lordswift/BambuHelper/src/clock_pong.h

#ifndef CLOCK_PONG_H
#define CLOCK_PONG_H

// Pong/Breakout animated clock - call tickPongClock() from loop()
void tickPongClock();

// Reset state (call when entering SCREEN_CLOCK)
void resetPongClock();

#endif // CLOCK_PONG_H
