lordswift/BambuHelper/src/display_ui.cpp

#include "display_ui.h"
#include "display_gauges.h"
#include "display_anim.h"
#include "clock_mode.h"
#include "clock_pong.h"
#include "icons.h"
#include "config.h"
#include "layout.h"
#include "bambu_state.h"
#include "bambu_mqtt.h"
#include "settings.h"
#include "tasmota.h"
#include <WiFi.h>
#include <time.h>

TFT_eSPI tft = TFT_eSPI();

// Use user-configured bg color instead of hardcoded CLR_BG
#undef  CLR_BG
#define CLR_BG  (dispSettings.bgColor)

static ScreenState currentScreen = SCREEN_SPLASH;
static ScreenState prevScreen = SCREEN_SPLASH;
static bool forceRedraw = true;
static unsigned long lastDisplayUpdate = 0;

// Previous state for smart redraw
static BambuState prevState;
static bool prevWaitingForDoor = false;
static unsigned long connectScreenStart = 0;

// ---------------------------------------------------------------------------
//  Smooth gauge interpolation - values lerp toward MQTT actuals each frame
// ---------------------------------------------------------------------------
static float smoothNozzleTemp   = 0;
static float smoothBedTemp      = 0;
static float smoothPartFan     = 0;
static float smoothAuxFan      = 0;
static float smoothChamberFan  = 0;
static float smoothChamberTemp = 0;
static float smoothHeatbreakFan= 0;
static bool  smoothInited      = false;

static bool gaugesAnimating = false;       // true while arcs are interpolating
static const unsigned long GAUGE_ANIM_MS = 80; // ~12 Hz during animation

static const float SMOOTH_ALPHA = 0.09f;  // per frame at 12Hz — ~1s to settle
static const float SNAP_THRESH  = 0.5f;   // snap when within 0.5 of target

static void smoothLerp(float& cur, float target) {
  float diff = target - cur;
  if (fabsf(diff) < SNAP_THRESH) cur = target;
  else cur += diff * SMOOTH_ALPHA;
}

// Returns true if any gauge is still animating
static bool tickGaugeSmooth(const BambuState& s, bool snap) {
  if (snap || !smoothInited) {
    smoothNozzleTemp   = s.nozzleTemp;
    smoothBedTemp      = s.bedTemp;
    smoothPartFan      = s.coolingFanPct;
    smoothAuxFan       = s.auxFanPct;
    smoothChamberFan   = s.chamberFanPct;
    smoothChamberTemp  = s.chamberTemp;
    smoothHeatbreakFan = s.heatbreakFanPct;
    smoothInited = true;
    return false;
  }
  smoothLerp(smoothNozzleTemp,   s.nozzleTemp);
  smoothLerp(smoothBedTemp,      s.bedTemp);
  smoothLerp(smoothPartFan,      (float)s.coolingFanPct);
  smoothLerp(smoothAuxFan,       (float)s.auxFanPct);
  smoothLerp(smoothChamberFan,   (float)s.chamberFanPct);
  smoothLerp(smoothChamberTemp,  s.chamberTemp);
  smoothLerp(smoothHeatbreakFan, (float)s.heatbreakFanPct);

  const float ANIM_EPS = 0.01f;
  return (fabsf(smoothNozzleTemp   - s.nozzleTemp)              > ANIM_EPS) ||
         (fabsf(smoothBedTemp      - s.bedTemp)                 > ANIM_EPS) ||
         (fabsf(smoothPartFan      - (float)s.coolingFanPct)    > ANIM_EPS) ||
         (fabsf(smoothAuxFan       - (float)s.auxFanPct)        > ANIM_EPS) ||
         (fabsf(smoothChamberFan   - (float)s.chamberFanPct)    > ANIM_EPS) ||
         (fabsf(smoothChamberTemp  - s.chamberTemp)             > ANIM_EPS) ||
         (fabsf(smoothHeatbreakFan - (float)s.heatbreakFanPct)  > ANIM_EPS);
}

// ---------------------------------------------------------------------------
//  Backlight
// ---------------------------------------------------------------------------
static uint8_t lastAppliedBrightness = 0;

void setBacklight(uint8_t level) {
#if defined(BACKLIGHT_PIN) && BACKLIGHT_PIN >= 0
#if defined(DISPLAY_1_8)
  digitalWrite(BACKLIGHT_PIN, level > 0 ? LOW : HIGH);  // Active low backlight
#else
  analogWrite(BACKLIGHT_PIN, level);
#endif
#endif
  lastAppliedBrightness = level;
}

// ---------------------------------------------------------------------------
//  Init
// ---------------------------------------------------------------------------
void initDisplay() {
  Serial.println("Display: pre-init delay...");
  delay(500);
  Serial.println("Display: calling tft.init()...");
  Serial.flush();
  tft.init();  // TFT_eSPI configures SPI from build flags
  Serial.println("Display: tft.init() done");
#if defined(DISPLAY_CYD)
  // Clear entire GRAM at rotation 0 first (guarantees all 240x320 pixels
  // are addressed). Without this, rotations 1/3 leave 80px of uninitialized
  // VRAM visible as garbage noise on the extra screen edge.
  tft.setRotation(0);
  tft.fillScreen(TFT_BLACK);
#endif
  tft.setRotation(dispSettings.rotation);
#if defined(DISPLAY_CYD)
  if (dispSettings.invertColors) tft.invertDisplay(false);
#endif
  Serial.println("Display: setRotation done");
  tft.fillScreen(CLR_BG);
  Serial.println("Display: fillScreen done");

#if defined(TOUCH_CS) && !defined(USE_XPT2046)
  uint16_t calData[5] = {321, 3498, 280, 3584, 3};
  tft.setTouch(calData);
  Serial.println("Display: touch calibration set");
#endif

#if defined(BACKLIGHT_PIN) && BACKLIGHT_PIN >= 0
  pinMode(BACKLIGHT_PIN, OUTPUT);
  setBacklight(200);
#endif

  memset(&prevState, 0, sizeof(prevState));

  // Splash screen
  tft.setTextDatum(MC_DATUM);
  tft.setTextColor(CLR_GREEN, CLR_BG);
  tft.setTextFont(3);
  tft.drawString("BambuHelper", SCREEN_W / 2, SCREEN_H / 2 - 24);
  tft.setTextFont(2);
  tft.setTextColor(CLR_TEXT_DIM, CLR_BG);
  tft.drawString("Printer Monitor", SCREEN_W / 2, SCREEN_H / 2 - 2);
  tft.setTextFont(1);
  tft.drawString(FW_VERSION, SCREEN_W / 2, SCREEN_H / 2 + 16);
}

void applyDisplaySettings() {
#if defined(DISPLAY_CYD)
  // Pre-clear entire GRAM at rotation 0 to prevent garbage on edges
  tft.setRotation(0);
  tft.fillScreen(TFT_BLACK);
#endif
  tft.setRotation(dispSettings.rotation);
#if defined(DISPLAY_CYD)
  tft.invertDisplay(dispSettings.invertColors ? false : true);
#endif
  tft.fillScreen(dispSettings.bgColor);
  forceRedraw = true;
  lastDisplayUpdate = 0;  // bypass throttle so redraw is immediate after fillScreen
  // Reset clock/pong so they redraw fully after fillScreen cleared everything
  if (currentScreen == SCREEN_CLOCK) {
    if (dispSettings.pongClock) resetPongClock();
    else resetClock();
  }
}

void triggerDisplayTransition() {
  // Clear previous state so everything redraws for the new printer
  memset(&prevState, 0, sizeof(prevState));
  smoothInited = false;  // snap gauges to new printer's values
  resetGaugeTextCache();
  tft.fillScreen(dispSettings.bgColor);
  forceRedraw = true;
}

void setScreenState(ScreenState state) {
  currentScreen = state;
}

ScreenState getScreenState() {
  return currentScreen;
}

// ---------------------------------------------------------------------------
//  Nozzle label helper (dual nozzle H2D/H2C)
// ---------------------------------------------------------------------------
static const char* nozzleLabel(const BambuState& s) {
  if (!s.dualNozzle) return "Nozzle";
  return s.activeNozzle == 0 ? "Nozzle R" : "Nozzle L";
}

// ---------------------------------------------------------------------------
//  Speed level name helper
// ---------------------------------------------------------------------------
static const char* speedLevelName(uint8_t level) {
  switch (level) {
    case 1: return "Silent";
    case 2: return "Std";
    case 3: return "Sport";
    case 4: return "Ludicr";
    default: return "---";
  }
}

static uint16_t speedLevelColor(uint8_t level) {
  switch (level) {
    case 1: return CLR_BLUE;
    case 2: return CLR_GREEN;
    case 3: return CLR_ORANGE;
    case 4: return CLR_RED;
    default: return CLR_TEXT_DIM;
  }
}

// ---------------------------------------------------------------------------
//  Screen: AP Mode
// ---------------------------------------------------------------------------
static void drawAPMode() {
  tft.setTextDatum(MC_DATUM);

  // Title
  tft.setTextColor(CLR_GREEN, CLR_BG);
  tft.setTextFont(3);
  tft.drawString("WiFi Setup", SCREEN_W / 2, LY_AP_TITLE_Y);

  // Instructions
  tft.setTextFont(1);
  tft.setTextColor(CLR_TEXT, CLR_BG);
  tft.drawString("Connect to WiFi:", SCREEN_W / 2, LY_AP_SSID_LBL_Y);

  // AP SSID
  tft.setTextColor(CLR_CYAN, CLR_BG);
  tft.setTextFont(3);
  char ssid[32];
  uint32_t mac = (uint32_t)(ESP.getEfuseMac() & 0xFFFF);
  snprintf(ssid, sizeof(ssid), "%s%04X", WIFI_AP_PREFIX, mac);
  tft.drawString(ssid, SCREEN_W / 2, LY_AP_SSID_Y);

  // Password
  tft.setTextFont(1);
  tft.setTextColor(CLR_TEXT_DIM, CLR_BG);
  tft.drawString("Password:", SCREEN_W / 2, LY_AP_PASS_LBL_Y);
  tft.setTextColor(CLR_TEXT, CLR_BG);
  tft.drawString(WIFI_AP_PASSWORD, SCREEN_W / 2, LY_AP_PASS_Y);

  // IP
  tft.setTextColor(CLR_TEXT_DIM, CLR_BG);
  tft.drawString("Then open:", SCREEN_W / 2, LY_AP_OPEN_Y);
  tft.setTextColor(CLR_ORANGE, CLR_BG);
  tft.setTextFont(3);
  tft.drawString("192.168.4.1", SCREEN_W / 2, LY_AP_IP_Y);
}

// ---------------------------------------------------------------------------
//  Screen: Connecting WiFi
// ---------------------------------------------------------------------------
static void drawConnectingWiFi() {
  tft.setTextDatum(MC_DATUM);

  // Title
  tft.setTextFont(1);
  tft.setTextColor(CLR_TEXT, CLR_BG);
  tft.drawString("Connecting to WiFi", SCREEN_W / 2, SCREEN_H / 2 - 24);

  int16_t tw = tft.textWidth("Connecting to WiFi");
  drawAnimDots(tft, SCREEN_W / 2 + tw / 2, SCREEN_H / 2 - 30, CLR_TEXT);

  // Slide bar
  const int16_t barW = 96;
  const int16_t barH = 6;
  drawSlideBar(tft, (SCREEN_W - barW) / 2, SCREEN_H / 2 + 12,
               barW, barH, CLR_BLUE, CLR_TRACK);
}

// ---------------------------------------------------------------------------
//  Screen: WiFi Connected (show IP)
// ---------------------------------------------------------------------------
static void drawWiFiConnected() {
  if (!forceRedraw) return;

  tft.setTextDatum(MC_DATUM);

  // Checkmark circle with tick
  int cx = SCREEN_W / 2;
  int cy = SCREEN_H / 2 - 40;
  tft.fillCircle(cx, cy, 18, CLR_GREEN);
  // Draw thick tick mark (2px wide)
  for (int i = -1; i <= 1; i++) {
    tft.drawLine(cx - 12, cy + i,     cx - 4, cy + 8 + i, CLR_BG);  // short leg
    tft.drawLine(cx - 4,  cy + 8 + i, cx + 12, cy - 6 + i, CLR_BG); // long leg
  }

  tft.setTextColor(CLR_GREEN, CLR_BG);
  tft.setTextFont(3);
  tft.drawString("WiFi Connected", SCREEN_W / 2, SCREEN_H / 2 + 8);

  tft.setTextColor(CLR_TEXT, CLR_BG);
  tft.setTextFont(1);
  tft.drawString(WiFi.localIP().toString().c_str(), SCREEN_W / 2, SCREEN_H / 2 + 28);
}

// ---------------------------------------------------------------------------
//  Screen: OTA firmware update in progress
// ---------------------------------------------------------------------------
#ifdef ENABLE_OTA_AUTO
#include "web_server.h"
static void drawOtaUpdate() {
  tft.setTextDatum(MC_DATUM);
  tft.setTextColor(CLR_TEXT, CLR_BG);

  // Title
  tft.setTextFont(3);
  tft.drawString("Updating", SCREEN_W / 2, SCREEN_H / 2 - 50);
  tft.setTextFont(2);
  tft.setTextColor(CLR_TEXT_DIM, CLR_BG);
  tft.drawString("BambuHelper firmware", SCREEN_W / 2, SCREEN_H / 2 - 26);

  // Progress bar
  int pct = getOtaAutoProgress();
  const int16_t barX = 16, barY = SCREEN_H / 2 - 8;
  const int16_t barW = SCREEN_W - 32, barH = 10;
  tft.fillRoundRect(barX, barY, barW, barH, 4, CLR_TRACK);
  if (pct > 0) {
    int16_t fill = (int16_t)((pct / 100.0f) * barW);
    tft.fillRoundRect(barX, barY, fill, barH, 4, CLR_GREEN);
  }

  // Percentage
  char pctBuf[8];
  snprintf(pctBuf, sizeof(pctBuf), "%d%%", pct);
  tft.setTextFont(2);
  tft.setTextColor(CLR_TEXT, CLR_BG);
  tft.drawString(pctBuf, SCREEN_W / 2, SCREEN_H / 2 + 14);

  // Status
  tft.setTextFont(2);
  tft.setTextColor(CLR_TEXT_DIM, CLR_BG);
  tft.drawString(getOtaAutoStatus(), SCREEN_W / 2, SCREEN_H / 2 + 34);

  // Warning
  tft.setTextColor(CLR_ORANGE, CLR_BG);
  tft.drawString("Do not power off", SCREEN_W / 2, SCREEN_H / 2 + 58);
}
#endif // ENABLE_OTA_AUTO

// ---------------------------------------------------------------------------
//  Screen: Connecting MQTT
// ---------------------------------------------------------------------------
static void drawConnectingMQTT() {
  tft.setTextDatum(MC_DATUM);

  // Title
  tft.setTextFont(2);
  tft.setTextColor(CLR_TEXT, CLR_BG);
  tft.drawString("Connecting to Printer", SCREEN_W / 2, SCREEN_H / 2 - 40);

  int16_t tw = tft.textWidth("Connecting to Printer");
  drawAnimDots(tft, SCREEN_W / 2 + tw / 2, SCREEN_H / 2 - 46, CLR_TEXT);
  tft.setTextDatum(MC_DATUM);

  // Slide bar
  const int16_t barW = 96;
  const int16_t barH = 6;
  drawSlideBar(tft, (SCREEN_W - barW) / 2, SCREEN_H / 2 - 12,
               barW, barH, CLR_ORANGE, CLR_TRACK);

  // Connection mode + printer info
  PrinterSlot& p = displayedPrinter();
  tft.setTextColor(CLR_TEXT_DIM, CLR_BG);
  tft.setTextFont(2);

  const char* modeStr = isCloudMode(p.config.mode) ? "Cloud" : "LAN";
  char infoBuf[40];
  if (isCloudMode(p.config.mode)) {
    snprintf(infoBuf, sizeof(infoBuf), "[%s] %s", modeStr,
             strlen(p.config.serial) > 0 ? p.config.serial : "no serial!");
  } else {
    snprintf(infoBuf, sizeof(infoBuf), "[%s] %s",  modeStr,
             strlen(p.config.ip) > 0 ? p.config.ip : "no IP!");
  }
  tft.drawString(infoBuf, SCREEN_W / 2, SCREEN_H / 2 + 10);

  // Elapsed time
  if (connectScreenStart > 0) {
    unsigned long elapsed = (millis() - connectScreenStart) / 1000;
    char elBuf[16];
    snprintf(elBuf, sizeof(elBuf), "%lus", elapsed);
    tft.fillRect(SCREEN_W / 2 - 30, SCREEN_H / 2 + 22, 60, 16, CLR_BG);
    tft.drawString(elBuf, SCREEN_W / 2, SCREEN_H / 2 + 30);
  }

  // Diagnostics (only after first attempt)
  const MqttDiag& d = getMqttDiag(rotState.displayIndex);
  if (d.attempts > 0) {
    tft.setTextFont(1);
    tft.setTextDatum(MC_DATUM);

    char buf[40];
    snprintf(buf, sizeof(buf), "Attempt: %u", d.attempts);
    tft.setTextColor(CLR_TEXT_DIM, CLR_BG);
    tft.drawString(buf, SCREEN_W / 2, SCREEN_H / 2 + 50);

    if (d.lastRc != 0) {
      snprintf(buf, sizeof(buf), "Err: %s", mqttRcToString(d.lastRc));
      tft.setTextColor(CLR_RED, CLR_BG);
      tft.drawString(buf, SCREEN_W / 2, SCREEN_H / 2 + 62);
    }
  }
}

// Forward declaration (defined after CYD section)
static void drawWifiSignalIndicator(const BambuState& s, int16_t wifiY);

// ---------------------------------------------------------------------------
//  Screen: Idle (connected, not printing)
// ---------------------------------------------------------------------------
static void drawIdleNoPrinter() {
  if (!forceRedraw) return;

  tft.setTextDatum(MC_DATUM);

  tft.setTextColor(CLR_GREEN, CLR_BG);
  tft.setTextFont(3);
  tft.drawString("BambuHelper", SCREEN_W / 2, LY_IDLE_NP_TITLE_Y);

  tft.setTextColor(CLR_TEXT, CLR_BG);
  tft.setTextFont(2);
  tft.drawString("WiFi Connected", SCREEN_W / 2, LY_IDLE_NP_WIFI_Y);

  tft.fillCircle(SCREEN_W / 2, LY_IDLE_NP_DOT_Y, 5, CLR_GREEN);

  tft.setTextColor(CLR_TEXT_DIM, CLR_BG);
  tft.setTextFont(1);
  tft.drawString("No printer configured", SCREEN_W / 2, LY_IDLE_NP_MSG_Y);
  tft.drawString("Open in browser:", SCREEN_W / 2, LY_IDLE_NP_OPEN_Y);

  tft.setTextColor(CLR_ORANGE, CLR_BG);
  tft.setTextFont(3);
  tft.drawString(WiFi.localIP().toString().c_str(), SCREEN_W / 2, LY_IDLE_NP_IP_Y);
}

static bool wasNoPrinter = false;

static void drawIdle() {
  if (!isAnyPrinterConfigured()) {
    wasNoPrinter = true;
    drawIdleNoPrinter();
    return;
  }

  // Transition from "no printer" to configured — clear stale screen
  if (wasNoPrinter) {
    wasNoPrinter = false;
    tft.fillScreen(dispSettings.bgColor);
    memset(&prevState, 0, sizeof(prevState));
    forceRedraw = true;
  }

  PrinterSlot& p = displayedPrinter();
  BambuState& s = p.state;

  // Effective screen dimensions — idle uses full screen (no AMS sidebar)
#if defined(DISPLAY_CYD)
  const int16_t scrW = (int16_t)tft.width();
  const int16_t scrH = (int16_t)tft.height();
#else
  const int16_t scrW = SCREEN_W;
  const int16_t scrH = SCREEN_H;
#endif
  const int16_t cx = scrW / 2;

  bool animating = tickGaugeSmooth(s, forceRedraw);
  gaugesAnimating = animating;
  bool stateChanged = forceRedraw || (strcmp(s.gcodeState, prevState.gcodeState) != 0);
  bool tempChanged = forceRedraw || animating ||
                     (s.nozzleTemp != prevState.nozzleTemp) ||
                     (s.nozzleTarget != prevState.nozzleTarget) ||
                     (s.bedTemp != prevState.bedTemp) ||
                     (s.bedTarget != prevState.bedTarget);
  bool connChanged = forceRedraw || (s.connected != prevState.connected);
  bool wifiChanged = forceRedraw || (s.wifiSignal != prevState.wifiSignal);

  tft.setTextDatum(MC_DATUM);

  // Printer name (only on forceRedraw — name doesn't change)
  if (forceRedraw) {
    tft.setTextColor(CLR_GREEN, CLR_BG);
    tft.setTextFont(4);
    const char* name = (p.config.name[0] != '\0') ? p.config.name : "Bambu P1S";
    tft.drawString(name, cx, LY_IDLE_NAME_Y);
  }

  // Status badge — only redraw when state changes
  if (stateChanged) {
    tft.setTextFont(2);
    uint16_t stateColor = CLR_TEXT_DIM;
    const char* stateStr = s.gcodeState;
    if (strcmp(s.gcodeState, "IDLE") == 0) {
      stateColor = CLR_GREEN;
      stateStr = "Ready";
    } else if (strcmp(s.gcodeState, "FAILED") == 0) {
      stateColor = CLR_RED;
      stateStr = "ERROR";
    } else if (strcmp(s.gcodeState, "UNKNOWN") == 0 || s.gcodeState[0] == '\0') {
      stateStr = "Waiting...";
    }
    tft.fillRect(0, LY_IDLE_STATE_Y, scrW, LY_IDLE_STATE_H, CLR_BG);
    tft.setTextColor(stateColor, CLR_BG);
    tft.drawString(stateStr, cx, LY_IDLE_STATE_TY);
  }

  // Connected indicator
  if (connChanged) {
    tft.fillCircle(cx, LY_IDLE_DOT_Y, 5, s.connected ? CLR_GREEN : CLR_RED);
  }

  // "Press to refresh" hint for cloud printers stuck in UNKNOWN state
  {
    static unsigned long unknownSinceMs = 0;
    static bool hintShown = false;
    bool isUnknown = (strcmp(s.gcodeState, "UNKNOWN") == 0);
    if (isUnknown && unknownSinceMs == 0) unknownSinceMs = millis();
    if (!isUnknown) unknownSinceMs = 0;
    bool showHint = isUnknown && unknownSinceMs > 0 &&
                    millis() - unknownSinceMs > 60000 &&
                    buttonType != BTN_DISABLED &&
                    isCloudMode(p.config.mode) && s.connected;
    if (stateChanged || showHint != hintShown) {
      const int16_t hintY = LY_IDLE_DOT_Y + 15;
      tft.fillRect(0, hintY - 6, scrW, 14, CLR_BG);
      if (showHint) {
        tft.setTextFont(1);
        tft.setTextDatum(MC_DATUM);
        tft.setTextColor(CLR_TEXT_DARK, CLR_BG);
        tft.drawString("Press to refresh", cx, hintY);
      }
      hintShown = showHint;
    }
  }

  // Nozzle temp gauge
  if (tempChanged) {
    drawTempGauge(tft, cx - LY_IDLE_G_OFFSET, LY_IDLE_GAUGE_Y, LY_IDLE_GAUGE_R,
                  s.nozzleTemp, s.nozzleTarget, 300.0f,
                  dispSettings.nozzle.arc, nozzleLabel(s), nullptr, forceRedraw,
                  &dispSettings.nozzle, smoothNozzleTemp);

    // Bed temp gauge
    drawTempGauge(tft, cx + LY_IDLE_G_OFFSET, LY_IDLE_GAUGE_Y, LY_IDLE_GAUGE_R,
                  s.bedTemp, s.bedTarget, 120.0f,
                  dispSettings.bed.arc, "Bed", nullptr, forceRedraw,
                  &dispSettings.bed, smoothBedTemp);
  }

  // Bottom status bar: Filament/WiFi | Power | Door
  static bool     idlePrevTasmotaOnline = false;
  static float    idlePrevWatts        = -2.0f;

  bool idleTasmotaOnline = tasmotaIsActiveForSlot(rotState.displayIndex);
  float idleCurWatts = tasmotaGetWatts();

  int16_t botCY = scrH - 9;
  bool bottomChanged = wifiChanged ||
                       (s.ams.activeTray != prevState.ams.activeTray) ||
                       (s.doorOpen != prevState.doorOpen) ||
                       (s.doorSensorPresent != prevState.doorSensorPresent) ||
                       (tasmotaSettings.enabled && (idleTasmotaOnline != idlePrevTasmotaOnline ||
                                                    idleCurWatts != idlePrevWatts));
  idlePrevTasmotaOnline  = idleTasmotaOnline;
  idlePrevWatts          = idleCurWatts;

  if (bottomChanged) {
    tft.fillRect(0, scrH - 18, scrW, 18, CLR_BG);
    tft.setTextFont(2);

    // Left: filament circle (if AMS active) or WiFi signal
    if (s.ams.present && s.ams.activeTray < AMS_MAX_TRAYS && s.ams.trays[s.ams.activeTray].present) {
      AmsTray& t = s.ams.trays[s.ams.activeTray];
      tft.drawCircle(10, botCY, 5, CLR_TEXT_DARK);
      tft.fillCircle(10, botCY, 4, t.colorRgb565);
      tft.setTextDatum(ML_DATUM);
      tft.setTextColor(CLR_TEXT_DIM, CLR_BG);
      tft.drawString(t.type, 19, botCY);
    } else if (s.ams.vtPresent && s.ams.activeTray == 254) {
      tft.drawCircle(10, botCY, 5, CLR_TEXT_DARK);
      tft.fillCircle(10, botCY, 4, s.ams.vtColorRgb565);
      tft.setTextDatum(ML_DATUM);
      tft.setTextColor(CLR_TEXT_DIM, CLR_BG);
      tft.drawString(s.ams.vtType, 19, botCY);
    } else {
      drawWifiSignalIndicator(s, botCY);
    }

    // Center: power watts (if Tasmota online)
    // Ready screen has no layer count, so always show power (no alternation)
    bool showPower = idleTasmotaOnline;
    if (showPower) {
      drawIcon16(tft, cx - 20, botCY - 8, icon_lightning, CLR_YELLOW);
      char wBuf[8];
      snprintf(wBuf, sizeof(wBuf), "%.0fW", tasmotaGetWatts());
      tft.setTextDatum(ML_DATUM);
      tft.setTextColor(CLR_TEXT_DIM, CLR_BG);
      tft.drawString(wBuf, cx - 2, botCY);
    }

    // Right: door status (if sensor present)
    if (s.doorSensorPresent) {
      uint16_t clr = s.doorOpen ? CLR_ORANGE : CLR_GREEN;
      tft.setTextDatum(MR_DATUM);
      tft.setTextColor(clr, CLR_BG);
      tft.drawString("Door", scrW - 20, botCY);
      drawIcon16(tft, scrW - 18, botCY - 8,
                 s.doorOpen ? icon_unlock : icon_lock, clr);
    }
  }
}

// ---------------------------------------------------------------------------
//  AMS tray visualization (CYD only)
//  Portrait: horizontal strip between gauges and ETA (y=190-246)
//  Landscape: vertical strip on right side (x=244-316)
// ---------------------------------------------------------------------------
#if defined(DISPLAY_CYD)

static bool cydLandscape() {
  return (dispSettings.rotation == 1 || dispSettings.rotation == 3);
}

static uint8_t  prevAmsUnitCount = 0;
static uint8_t  prevAmsActive    = 255;
static uint16_t prevAmsTrayColors[AMS_MAX_TRAYS] = {0};
static bool     prevAmsTrayPresent[AMS_MAX_TRAYS] = {false};

// Helper: draw a single AMS tray bar (used by both portrait and landscape)
static void drawAmsTrayBar(int16_t x, int16_t y, int16_t w, int16_t h,
                           const AmsTray& tray, bool isActive) {
  if (tray.present) {
    if (isActive) {
      tft.fillRect(x, y, w, h, TFT_WHITE);
      tft.fillRect(x + 2, y + 2, w - 4, h - 4, tray.colorRgb565);
    } else {
      tft.drawRect(x, y, w, h, CLR_TEXT_DARK);
      tft.fillRect(x + 1, y + 1, w - 2, h - 2, tray.colorRgb565);
    }
  } else {
    // Empty slot: outline + diagonal cross to distinguish from black filament
    tft.drawRect(x, y, w, h, CLR_TEXT_DARK);
    tft.drawLine(x, y, x + w - 1, y + h - 1, CLR_TEXT_DARK);
    tft.drawLine(x + w - 1, y, x, y + h - 1, CLR_TEXT_DARK);
  }
}

static void drawAmsZone(const BambuState& s, bool force) {
  // --- Change detection ---
  bool changed = force;
  if (!changed) {
    changed = (s.ams.unitCount != prevAmsUnitCount) ||
              (s.ams.activeTray != prevAmsActive);
    if (!changed) {
      for (uint8_t i = 0; i < s.ams.unitCount * AMS_TRAYS_PER_UNIT && !changed; i++) {
        changed = (s.ams.trays[i].present != prevAmsTrayPresent[i]) ||
                  (s.ams.trays[i].colorRgb565 != prevAmsTrayColors[i]);
      }
    }
  }
  if (!changed) return;

  // Save state for next comparison
  prevAmsUnitCount = s.ams.unitCount;
  prevAmsActive    = s.ams.activeTray;
  for (uint8_t i = 0; i < AMS_MAX_TRAYS; i++) {
    prevAmsTrayPresent[i] = s.ams.trays[i].present;
    prevAmsTrayColors[i]  = s.ams.trays[i].colorRgb565;
  }

  uint8_t units = s.ams.unitCount;
  bool landscape = cydLandscape();

  if (landscape) {
    // =====================================================================
    //  LANDSCAPE: vertical strip on right side (x=244, 72px wide)
    //  AMS groups stacked vertically, each group has 4 VERTICAL bars
    //  side-by-side (same orientation as portrait / physical AMS)
    // =====================================================================
    tft.fillRect(LY_LAND_AMS_X - 4, LY_LAND_AMS_TOP, LY_LAND_AMS_W + 8,
                 LY_LAND_AMS_BOT - LY_LAND_AMS_TOP, CLR_BG);

    if (units == 0 || units > AMS_MAX_UNITS) return;

    const int16_t totalH = LY_LAND_AMS_BOT - LY_LAND_AMS_TOP;  // ~208px
    const int16_t groupGap = 6;
    const int16_t labelH = 12;  // space for AMS letter label below bars
    const int16_t barGap = 2;   // gap between bars

    // 4 vertical bars side-by-side in the 72px width
    int16_t barW = (LY_LAND_AMS_W - (AMS_TRAYS_PER_UNIT - 1) * barGap) / AMS_TRAYS_PER_UNIT;
    if (barW > 16) barW = 16;
    if (barW < 4) barW = 4;

    // Calculate group height: bar height + label
    int16_t groupH = (totalH - (units - 1) * groupGap) / units;
    int16_t barH = groupH - labelH;
    if (barH > 50) barH = 50;
    if (barH < 10) barH = 10;

    // Center everything
    int16_t actualGroupW = barW * AMS_TRAYS_PER_UNIT + (AMS_TRAYS_PER_UNIT - 1) * barGap;
    int16_t barsX = LY_LAND_AMS_X + (LY_LAND_AMS_W - actualGroupW) / 2;
    int16_t actualGroupH = barH + labelH;
    int16_t totalUsed = actualGroupH * units + (units - 1) * groupGap;
    int16_t startY = LY_LAND_AMS_TOP + (totalH - totalUsed) / 2;

    for (uint8_t u = 0; u < units; u++) {
      int16_t gy = startY + u * (actualGroupH + groupGap);

      // 4 vertical bars side-by-side
      for (uint8_t t = 0; t < AMS_TRAYS_PER_UNIT; t++) {
        uint8_t trayIdx = u * AMS_TRAYS_PER_UNIT + t;
        int16_t bx = barsX + t * (barW + barGap);
        drawAmsTrayBar(bx, gy, barW, barH,
                       s.ams.trays[trayIdx], trayIdx == s.ams.activeTray);
      }

      // AMS label below bars
      char label[6];
      snprintf(label, sizeof(label), "AMS %c", 'A' + u);
      tft.setTextDatum(TC_DATUM);
      bool sm = dispSettings.smallLabels;
      tft.setTextFont(sm ? 1 : 2);
      tft.setTextColor(CLR_TEXT_DIM, CLR_BG);
      tft.drawString(label, LY_LAND_AMS_X + LY_LAND_AMS_W / 2, gy + barH + 2);
    }

  } else {
    // =====================================================================
    //  PORTRAIT: horizontal strip between gauges and ETA (y=190-246)
    //  AMS groups side by side, each with 4 vertical bars
    // =====================================================================
    tft.fillRect(0, LY_AMS_Y, LY_W, LY_AMS_H, CLR_BG);

    if (units == 0 || units > AMS_MAX_UNITS) return;

    const int16_t usableW = LY_W - 2 * LY_AMS_MARGIN;
    int16_t groupW = (usableW - (units - 1) * LY_AMS_GROUP_GAP) / units;
    int16_t barW = (groupW - (AMS_TRAYS_PER_UNIT - 1) * LY_AMS_BAR_GAP) / AMS_TRAYS_PER_UNIT;
    if (barW > LY_AMS_BAR_MAX_W) barW = LY_AMS_BAR_MAX_W;
    if (barW < 4) barW = 4;

    int16_t actualGroupW = barW * AMS_TRAYS_PER_UNIT + (AMS_TRAYS_PER_UNIT - 1) * LY_AMS_BAR_GAP;
    int16_t totalW = actualGroupW * units + (units - 1) * LY_AMS_GROUP_GAP;
    int16_t startX = (LY_W - totalW) / 2;

    int16_t barY = LY_AMS_Y + (LY_AMS_H - LY_AMS_BAR_H - LY_AMS_LABEL_OFFY - 8) / 2;
    int16_t labelY = barY + LY_AMS_BAR_H + LY_AMS_LABEL_OFFY;

    for (uint8_t u = 0; u < units; u++) {
      int16_t groupX = startX + u * (actualGroupW + LY_AMS_GROUP_GAP);

      for (uint8_t t = 0; t < AMS_TRAYS_PER_UNIT; t++) {
        uint8_t trayIdx = u * AMS_TRAYS_PER_UNIT + t;
        int16_t bx = groupX + t * (barW + LY_AMS_BAR_GAP);
        drawAmsTrayBar(bx, barY, barW, LY_AMS_BAR_H,
                       s.ams.trays[trayIdx], trayIdx == s.ams.activeTray);
      }

      char label[6];
      snprintf(label, sizeof(label), "AMS %c", 'A' + u);
      tft.setTextDatum(TC_DATUM);
      bool sm = dispSettings.smallLabels;
      tft.setTextFont(sm ? 1 : 2);
      tft.setTextColor(CLR_TEXT_DIM, CLR_BG);
      tft.drawString(label, groupX + actualGroupW / 2, labelY + 2);
    }
  }
}

#endif // DISPLAY_CYD

// ---------------------------------------------------------------------------
//  Helper: draw WiFi signal indicator in bottom-left corner
// ---------------------------------------------------------------------------
static void drawWifiSignalIndicator(const BambuState& s, int16_t wifiY = LY_WIFI_Y) {
  drawIcon16(tft, LY_WIFI_X, wifiY - 8, icon_wifi, CLR_TEXT_DIM);
  tft.setTextDatum(ML_DATUM);
  tft.setTextColor(CLR_TEXT_DIM, CLR_BG);
  char wifiBuf[12];
  snprintf(wifiBuf, sizeof(wifiBuf), "%ddBm", s.wifiSignal);
  tft.drawString(wifiBuf, LY_WIFI_X + 18, wifiY);
}

// ---------------------------------------------------------------------------
//  Screen: Printing (main dashboard)
//  Layout: LED bar | header | 2x3 gauge grid | info line
// ---------------------------------------------------------------------------
static void drawPrinting() {
  PrinterSlot& p = displayedPrinter();
  BambuState& s = p.state;

  bool animating = tickGaugeSmooth(s, forceRedraw);
  gaugesAnimating = animating;
  bool progChanged = forceRedraw || (s.progress != prevState.progress);
  bool etaChanged = forceRedraw ||
                     (s.remainingMinutes != prevState.remainingMinutes);
  bool stateChanged = forceRedraw ||
                      (strcmp(s.gcodeState, prevState.gcodeState) != 0);

  // 2x3 gauge grid constants (from layout profile)
  const int16_t gR = LY_GAUGE_R;
  const int16_t gT = LY_GAUGE_T;

  // Effective Y positions — landscape on CYD uses 240x240-style positions
#if defined(DISPLAY_CYD)
  const bool land = cydLandscape();
  const int16_t eff_etaY     = land ? LY_LAND_ETA_Y     : LY_ETA_Y;
  const int16_t eff_etaH     = land ? LY_LAND_ETA_H     : LY_ETA_H;
  const int16_t eff_etaTextY = land ? LY_LAND_ETA_TEXT_Y : LY_ETA_TEXT_Y;
  const int16_t eff_botY     = land ? LY_LAND_BOT_Y     : LY_BOT_Y;
  const int16_t eff_botH     = land ? LY_LAND_BOT_H     : LY_BOT_H;
  const int16_t eff_botCY    = land ? LY_LAND_BOT_CY    : LY_BOT_CY;
#else
  const int16_t eff_etaY     = LY_ETA_Y;
  const int16_t eff_etaH     = LY_ETA_H;
  const int16_t eff_etaTextY = LY_ETA_TEXT_Y;
  const int16_t eff_botY     = LY_BOT_Y;
  const int16_t eff_botH     = LY_BOT_H;
  const int16_t eff_botCY    = LY_BOT_CY;
#endif

  // === CYD: clear unused zone on screen transitions ===
#if defined(DISPLAY_CYD)
  if (forceRedraw) {
    int16_t scrW = (int16_t)tft.width();
    int16_t scrH = (int16_t)tft.height();
    // Clear right edge if canvas wider than 240 (rotation 1/3)
    if (scrW > 240)
      tft.fillRect(240, 0, scrW - 240, scrH, CLR_BG);
    // Clear below content area if canvas taller than used
    int16_t usedBottom = eff_botY + eff_botH;
    if (usedBottom < scrH)
      tft.fillRect(0, usedBottom, scrW, scrH - usedBottom, CLR_BG);
  }
#endif

  // === H2-style LED progress bar (y=0-5) ===
  if (progChanged) {
    drawLedProgressBar(tft, 0, s.progress);
  }

  // === Header bar (y=7-25) ===
  if (forceRedraw || stateChanged) {
    uint16_t hdrBg = dispSettings.bgColor;
    tft.fillRect(0, LY_HDR_Y, SCREEN_W, LY_HDR_H, hdrBg);

    // Printer name (left)
    tft.setTextDatum(ML_DATUM);
    tft.setTextFont(2);
    tft.setTextColor(CLR_TEXT, hdrBg);
    const char* name = (p.config.name[0] != '\0') ? p.config.name : "Bambu P1S";
    tft.drawString(name, LY_HDR_NAME_X, LY_HDR_CY);

    // Current printing state below the name
    uint16_t badgeColor = CLR_TEXT_DIM;
    if (strcmp(s.gcodeState, "RUNNING") == 0) badgeColor = CLR_GREEN;
    else if (strcmp(s.gcodeState, "PAUSE") == 0) badgeColor = CLR_YELLOW;
    else if (strcmp(s.gcodeState, "FAILED") == 0) badgeColor = CLR_RED;
    else if (strcmp(s.gcodeState, "PREPARE") == 0) badgeColor = CLR_BLUE;

    tft.setTextDatum(ML_DATUM);
    tft.setTextFont(1);
    tft.setTextColor(badgeColor, hdrBg);
    tft.drawString(s.gcodeState, LY_HDR_NAME_X, LY_HDR_STATE_Y);

    // Progress percentage on the right side
    tft.setTextDatum(MR_DATUM);
    tft.setTextFont(2);
    tft.setTextColor(CLR_TEXT_DIM, hdrBg);
    char hdrProg[8];
    snprintf(hdrProg, sizeof(hdrProg), "%d%%", s.progress);
    int16_t progRightX = SCREEN_W - LY_HDR_BADGE_RX;
    int16_t progLeftX = progRightX - tft.textWidth(hdrProg) - 16;
    tft.fillCircle(progLeftX, LY_HDR_CY, 4, badgeColor);
    tft.drawString(hdrProg, progRightX, LY_HDR_CY);

    // Printer indicator dots (multi-printer)
    if (getActiveConnCount() > 1) {
      for (uint8_t di = 0; di < MAX_ACTIVE_PRINTERS; di++) {
        if (!isPrinterConfigured(di)) continue;
        uint16_t dotClr = (di == rotState.displayIndex) ? CLR_GREEN : CLR_TEXT_DARK;
        tft.fillCircle(SCREEN_W / 2 - 5 + di * 10, LY_HDR_DOT_CY, 3, dotClr);
      }
    }
  }

  // === Configurable 2x3 gauge grid ===
  {
    static unsigned long lastGaugeRotateMs = 0;
    static uint8_t currentGaugePage = 0;
    const bool rotateGauges = (SCREEN_W <= 128);
    const uint8_t visibleGaugeCount = 3;
    const uint8_t gaugePageCount = (GAUGE_SLOT_COUNT + visibleGaugeCount - 1) / visibleGaugeCount;
    bool pageChanged = false;
    if (rotateGauges && millis() - lastGaugeRotateMs > 3500) {
      lastGaugeRotateMs = millis();
      currentGaugePage = (currentGaugePage + 1) % gaugePageCount;
      pageChanged = true;
    }

    const int16_t pageX[3] = { 26, 102, 64 };
    const int16_t pageY[3] = { 48, 48, 100 };
    const int16_t pageR = rotateGauges ? 22 : gR;
    const int16_t pageT = gT;

    if (rotateGauges && (forceRedraw || pageChanged)) {
      tft.fillRect(0, LY_HDR_Y + LY_HDR_H, SCREEN_W,
                   eff_etaY - (LY_HDR_Y + LY_HDR_H), CLR_BG);
    }

    static uint8_t prevSlotTypes[GAUGE_SLOT_COUNT] = { 0xFF, 0xFF, 0xFF, 0xFF, 0xFF, 0xFF };

    for (uint8_t si = 0; si < GAUGE_SLOT_COUNT; si++) {
      uint8_t gt = p.config.gaugeSlots[si];
      if (gt >= GAUGE_TYPE_COUNT) gt = GAUGE_EMPTY;

      bool typeChanged = (gt != prevSlotTypes[si]);
      if (typeChanged) {
        prevSlotTypes[si] = gt;
      }

      const bool visibleThisPage = !rotateGauges ||
        (si >= currentGaugePage * visibleGaugeCount &&
         si < currentGaugePage * visibleGaugeCount + visibleGaugeCount);
      if (!visibleThisPage) {
        continue;
      }

      uint8_t pageIndex = si % visibleGaugeCount;
      int16_t cx = rotateGauges ? pageX[pageIndex] : (si < 3 ? LY_COL1 + si * (LY_COL2 - LY_COL1) : LY_COL1 + (si - 3) * (LY_COL2 - LY_COL1));
      int16_t cy = rotateGauges ? pageY[pageIndex] : (si < 3 ? LY_ROW1 : LY_ROW2);
      int16_t gaugeR = rotateGauges ? pageR : gR;
      int16_t gaugeT = rotateGauges ? pageT : gT;

      // Per-type change detection
      bool needDraw = forceRedraw || typeChanged || pageChanged;
      if (!needDraw) {
        switch (gt) {
          case GAUGE_PROGRESS:    needDraw = (s.progress != prevState.progress) || (s.remainingMinutes != prevState.remainingMinutes); break;
          case GAUGE_NOZZLE:      needDraw = animating || s.nozzleTemp != prevState.nozzleTemp || s.nozzleTarget != prevState.nozzleTarget; break;
          case GAUGE_BED:         needDraw = animating || s.bedTemp != prevState.bedTemp || s.bedTarget != prevState.bedTarget; break;
          case GAUGE_PART_FAN:    needDraw = animating || s.coolingFanPct != prevState.coolingFanPct; break;
          case GAUGE_AUX_FAN:     needDraw = animating || s.auxFanPct != prevState.auxFanPct; break;
          case GAUGE_CHAMBER_FAN: needDraw = animating || s.chamberFanPct != prevState.chamberFanPct; break;
          case GAUGE_CHAMBER_TEMP:needDraw = animating || s.chamberTemp != prevState.chamberTemp; break;
          case GAUGE_HEATBREAK:   needDraw = animating || s.heatbreakFanPct != prevState.heatbreakFanPct; break;
          case GAUGE_CLOCK:       needDraw = true; break;
          default: break;
        }
      }
      if (!needDraw) continue;

      bool fr = forceRedraw || typeChanged || pageChanged;

      switch (gt) {
        case GAUGE_PROGRESS:
          drawProgressArc(tft, cx, cy, gaugeR, gaugeT, s.progress, prevState.progress, s.remainingMinutes, fr);
          break;
        case GAUGE_NOZZLE:
          drawTempGauge(tft, cx, cy, gaugeR, s.nozzleTemp, s.nozzleTarget, 300.0f,
                        dispSettings.nozzle.arc, nozzleLabel(s), nullptr, fr,
                        &dispSettings.nozzle, smoothNozzleTemp);
          break;
        case GAUGE_BED:
          drawTempGauge(tft, cx, cy, gaugeR, s.bedTemp, s.bedTarget, 120.0f,
                        dispSettings.bed.arc, "Bed", nullptr, fr,
                        &dispSettings.bed, smoothBedTemp);
          break;
        case GAUGE_PART_FAN:
          drawFanGauge(tft, cx, cy, gaugeR, s.coolingFanPct, dispSettings.partFan.arc, "Part", fr,
                       &dispSettings.partFan, smoothPartFan);
          break;
        case GAUGE_AUX_FAN:
          drawFanGauge(tft, cx, cy, gaugeR, s.auxFanPct, dispSettings.auxFan.arc, "Aux", fr,
                       &dispSettings.auxFan, smoothAuxFan);
          break;
        case GAUGE_CHAMBER_FAN:
          drawFanGauge(tft, cx, cy, gaugeR, s.chamberFanPct, dispSettings.chamberFan.arc, "Chamber", fr,
                       &dispSettings.chamberFan, smoothChamberFan);
          break;
        case GAUGE_CHAMBER_TEMP:
          drawTempGauge(tft, cx, cy, gaugeR, s.chamberTemp, 0.0f, 60.0f,
                        dispSettings.chamberTemp.arc, "Chamber", nullptr, fr,
                        &dispSettings.chamberTemp, smoothChamberTemp);
          break;
        case GAUGE_HEATBREAK:
          drawFanGauge(tft, cx, cy, gaugeR, s.heatbreakFanPct, dispSettings.heatbreak.arc, "HBreak", fr,
                       &dispSettings.heatbreak, smoothHeatbreakFan);
          break;
        case GAUGE_CLOCK:
          drawClockWidget(tft, cx, cy, gaugeR, gaugeT, fr);
          break;
        case GAUGE_EMPTY:
        default:
          if (fr) tft.fillCircle(cx, cy, gaugeR + 2, dispSettings.bgColor);
          break;
      }
    }
  }

  // === AMS zone (CYD: portrait + landscape) ===
#if defined(DISPLAY_CYD)
  if (s.ams.present && s.ams.unitCount > 0) {
    drawAmsZone(s, forceRedraw);
  }
#endif

  // === Info line — ETA finish time or PAUSE/ERROR alert ===
  if (etaChanged || stateChanged) {
    tft.fillRect(0, eff_etaY, SCREEN_W, eff_etaH, CLR_BG);
    tft.setTextDatum(MC_DATUM);

    int16_t etaBarX = (SCREEN_W - LY_ETA_BAR_W) / 2;
    int16_t etaBarY = LY_ETA_BAR_Y;
    int16_t etaBarW = LY_ETA_BAR_W;
    int16_t etaBarH = LY_ETA_BAR_H;

    if (strcmp(s.gcodeState, "PAUSE") == 0) {
      tft.setTextFont(2);
      tft.setTextColor(CLR_YELLOW, CLR_BG);
      tft.drawString("PAUSED", SCREEN_W / 2, eff_etaTextY);
    } else if (strcmp(s.gcodeState, "FAILED") == 0) {
      tft.setTextFont(2);
      tft.setTextColor(CLR_RED, CLR_BG);
      tft.drawString("ERROR!", SCREEN_W / 2, eff_etaTextY);
    } else if (s.remainingMinutes > 0) {
      static bool ntpSynced = false;
      time_t nowEpoch = time(nullptr);
      struct tm now;
      localtime_r(&nowEpoch, &now);
      if (now.tm_year > (2020 - 1900)) ntpSynced = true;

      if (ntpSynced) {
        time_t etaEpoch = nowEpoch + (time_t)s.remainingMinutes * 60;
        struct tm etaTm;
        localtime_r(&etaEpoch, &etaTm);

        char etaTimeBuf[24];
        int etaH = etaTm.tm_hour;
        const char* ampm = "";
        if (!netSettings.use24h) {
          ampm = etaH < 12 ? "AM" : "PM";
          etaH = etaH % 12;
          if (etaH == 0) etaH = 12;
          snprintf(etaTimeBuf, sizeof(etaTimeBuf), "%d:%02d%s", etaH, etaTm.tm_min, ampm);
        } else {
          snprintf(etaTimeBuf, sizeof(etaTimeBuf), "%02d:%02d", etaH, etaTm.tm_min);
        }

        tft.setTextFont(3);
        tft.setTextColor(CLR_GREEN, CLR_BG);
        tft.drawString(etaTimeBuf, SCREEN_W / 2, eff_etaTextY - 2);

        tft.setTextFont(1);
        tft.setTextColor(CLR_TEXT_DIM, CLR_BG);
        tft.drawString("ETA", SCREEN_W / 2, eff_etaTextY + 8);
      } else {
        char remBuf[24];
        uint16_t h = s.remainingMinutes / 60;
        uint16_t m = s.remainingMinutes % 60;
        snprintf(remBuf, sizeof(remBuf), "%dh %02dm", h, m);

        tft.setTextFont(3);
        tft.setTextColor(CLR_TEXT, CLR_BG);
        tft.drawString(remBuf, SCREEN_W / 2, eff_etaTextY - 2);

        tft.setTextFont(1);
        tft.setTextColor(CLR_TEXT_DIM, CLR_BG);
        tft.drawString("Remain", SCREEN_W / 2, eff_etaTextY + 8);
      }

      uint16_t trackColor = dispSettings.trackColor;
      tft.fillRect(etaBarX, etaBarY, etaBarW, etaBarH, trackColor);
      int16_t fillW = (s.progress * etaBarW) / 100;
      if (fillW < 1) fillW = 1;
      tft.fillRect(etaBarX, etaBarY, fillW, etaBarH, dispSettings.progress.arc);
    } else {
      tft.setTextFont(3);
      tft.setTextColor(CLR_TEXT_DIM, CLR_BG);
      tft.drawString("---", SCREEN_W / 2, eff_etaTextY - 2);

      tft.setTextFont(1);
      tft.drawString("ETA", SCREEN_W / 2, eff_etaTextY + 8);

      uint16_t trackColor = dispSettings.trackColor;
      tft.fillRect(etaBarX, etaBarY, etaBarW, etaBarH, trackColor);
    }
  }

  // === Bottom status bar — Filament/WiFi | Layer (or Power) | Speed ===
  // Tasmota alternation state (persists across redraws)
  static bool     altShowPower    = false;
  static uint32_t altFlipMs       = 0;
  static bool     prevAltShowPower = false;
  static bool     prevTasmotaOnline = false;
  static float    prevWatts        = -2.0f;

  if (tasmotaSettings.enabled && tasmotaSettings.displayMode == 0) {
    if (millis() - altFlipMs > 4000) {
      altShowPower = !altShowPower;
      altFlipMs    = millis();
    }
  } else {
    altShowPower = false;
    altFlipMs    = 0;
  }
  bool tasmotaOnline = tasmotaIsActiveForSlot(rotState.displayIndex);
  float curWatts = tasmotaGetWatts();

  bool showingWifi = !(s.ams.present && s.ams.activeTray < AMS_MAX_TRAYS && s.ams.trays[s.ams.activeTray].present)
                  && !(s.ams.vtPresent && s.ams.activeTray == 254);
  bool bottomChanged = forceRedraw ||
                       (s.doorOpen != prevState.doorOpen) ||
                       (s.doorSensorPresent != prevState.doorSensorPresent) ||
                       (s.layerNum != prevState.layerNum) ||
                       (s.totalLayers != prevState.totalLayers) ||
                       (s.ams.activeTray != prevState.ams.activeTray) ||
                       (showingWifi && s.wifiSignal != prevState.wifiSignal) ||
                       (tasmotaSettings.enabled && (altShowPower != prevAltShowPower || tasmotaOnline != prevTasmotaOnline ||
                                                    curWatts != prevWatts));
  prevAltShowPower  = altShowPower;
  prevTasmotaOnline = tasmotaOnline;
  prevWatts         = curWatts;

  if (bottomChanged) {
    tft.fillRect(0, eff_botY, SCREEN_W, eff_botH, CLR_BG);
    tft.setTextFont(2);

    // Left: filament indicator (if AMS active) or WiFi signal
    // Dual nozzle (H2C/H2D): activeTray set from extruder.info[].snow per-nozzle
    if (s.ams.present && s.ams.activeTray < AMS_MAX_TRAYS) {
      AmsTray& t = s.ams.trays[s.ams.activeTray];
      if (t.present) {
        tft.drawCircle(10, eff_botCY, 5, CLR_TEXT_DARK);
        tft.fillCircle(10, eff_botCY, 4, t.colorRgb565);
        tft.setTextDatum(ML_DATUM);
        tft.setTextColor(CLR_TEXT_DIM, CLR_BG);
        tft.drawString(t.type, 19, eff_botCY);
      } else {
        drawWifiSignalIndicator(s, eff_botCY);
      }
    } else if (s.ams.vtPresent && s.ams.activeTray == 254) {
      tft.drawCircle(10, eff_botCY, 5, CLR_TEXT_DARK);
      tft.fillCircle(10, eff_botCY, 4, s.ams.vtColorRgb565);
      tft.setTextDatum(ML_DATUM);
      tft.setTextColor(CLR_TEXT_DIM, CLR_BG);
      tft.drawString(s.ams.vtType, 19, eff_botCY);
    } else {
      drawWifiSignalIndicator(s, eff_botCY);
    }

    // Center: power (if Tasmota active) or layer count
    bool showPowerNow = tasmotaSettings.enabled && tasmotaOnline &&
                        (tasmotaSettings.displayMode == 1 || altShowPower);
    if (showPowerNow) {
      drawIcon16(tft, SCREEN_W * 2 / 3 - 20, eff_botCY - 8, icon_lightning, CLR_YELLOW);
      char wBuf[8];
      snprintf(wBuf, sizeof(wBuf), "%.0fW", tasmotaGetWatts());
      tft.setTextDatum(ML_DATUM);
      tft.setTextColor(CLR_TEXT_DIM, CLR_BG);
      tft.drawString(wBuf, SCREEN_W * 2 / 3 - 2, eff_botCY);
    } else {
      tft.setTextDatum(MC_DATUM);
      tft.setTextColor(CLR_TEXT_DIM, CLR_BG);
      char layerBuf[20];
      snprintf(layerBuf, sizeof(layerBuf), "L%d/%d", s.layerNum, s.totalLayers);
      tft.drawString(layerBuf, SCREEN_W * 5 / 8, eff_botCY);
    }

    // Right: door status (if sensor present)
    if (s.doorSensorPresent) {
      uint16_t clr = s.doorOpen ? CLR_ORANGE : CLR_GREEN;
      tft.setTextDatum(MR_DATUM);
      tft.setTextColor(clr, CLR_BG);
      tft.drawString("Door", SCREEN_W - 20, eff_botCY);
      drawIcon16(tft, SCREEN_W - 18, eff_botCY - 8,
                 s.doorOpen ? icon_unlock : icon_lock, clr);
    }
  }
}

// ---------------------------------------------------------------------------
//  Screen: Finished (same layout as printing, but with 2 gauges + status)
// ---------------------------------------------------------------------------
static void drawFinished() {
  PrinterSlot& p = displayedPrinter();
  BambuState& s = p.state;
  static bool  prevFinTasmotaOnline = false;
  static float prevFinWatts = -2.0f;
  static float prevFinKwh = -2.0f;

  // Effective screen dimensions — finished uses full screen (no AMS sidebar)
#if defined(DISPLAY_CYD)
  const bool land = cydLandscape();
  const int16_t scrW = (int16_t)tft.width();
  const int16_t eff_finBotY  = land ? LY_LAND_FIN_BOT_Y  : LY_FIN_BOT_Y;
  const int16_t eff_finBotH  = land ? LY_LAND_FIN_BOT_H  : LY_FIN_BOT_H;
  const int16_t eff_finWifiY = land ? LY_LAND_FIN_WIFI_Y  : LY_FIN_WIFI_Y;
#else
  const int16_t scrW = SCREEN_W;
  const int16_t eff_finBotY  = LY_FIN_BOT_Y;
  const int16_t eff_finBotH  = LY_FIN_BOT_H;
  const int16_t eff_finWifiY = LY_FIN_WIFI_Y;
#endif
  const int16_t cx = scrW / 2;

  bool animating = tickGaugeSmooth(s, forceRedraw);
  bool tempChanged = forceRedraw || animating ||
                     (s.nozzleTemp != prevState.nozzleTemp) ||
                     (s.nozzleTarget != prevState.nozzleTarget) ||
                     (s.bedTemp != prevState.bedTemp) ||
                     (s.bedTarget != prevState.bedTarget);

  const int16_t gR = LY_FIN_GAUGE_R;
  const int16_t gaugeLeft  = LY_FIN_GL;
  const int16_t gaugeRight = LY_FIN_GR;
  const int16_t gaugeY = LY_FIN_GY;

  // === H2-style LED progress bar at 100% (y=0-5) ===
  if (forceRedraw) {
    drawLedProgressBar(tft, 0, 100);
    tft.setTextDatum(MC_DATUM);
    tft.setTextFont(2);
    tft.setTextColor(CLR_TEXT, dispSettings.bgColor);
    tft.drawString("100%", scrW / 2, LY_HDR_Y + 10);
  }

  // === Header bar (y=7-25) — same as printing screen ===
  if (forceRedraw) {
    uint16_t hdrBg = dispSettings.bgColor;
    tft.fillRect(0, LY_HDR_Y, scrW, LY_HDR_H, hdrBg);

    // Printer name (left)
    tft.setTextDatum(ML_DATUM);
    tft.setTextFont(2);
    tft.setTextColor(CLR_TEXT, hdrBg);
    const char* name = (p.config.name[0] != '\0') ? p.config.name : "Printer";
    tft.drawString(name, LY_HDR_NAME_X, LY_HDR_CY);

    // FINISH badge (right)
    tft.setTextDatum(MR_DATUM);
    tft.setTextColor(CLR_GREEN, hdrBg);
    tft.setTextFont(2);
    tft.fillCircle(scrW - LY_HDR_BADGE_RX - tft.textWidth("FINISH") - 10, LY_HDR_CY, 4, CLR_GREEN);
    tft.drawString("FINISH", scrW - LY_HDR_BADGE_RX, LY_HDR_CY);

    // Printer indicator dots (multi-printer)
    if (getActiveConnCount() > 1) {
      for (uint8_t di = 0; di < MAX_ACTIVE_PRINTERS; di++) {
        if (!isPrinterConfigured(di)) continue;
        uint16_t dotClr = (di == rotState.displayIndex) ? CLR_GREEN : CLR_TEXT_DARK;
        tft.fillCircle(cx - 5 + di * 10, LY_HDR_DOT_CY, 3, dotClr);
      }
    }
  }

  // === Row 1: Nozzle | Bed (two gauges centered) ===
  if (tempChanged) {
    drawTempGauge(tft, gaugeLeft, gaugeY, gR,
                  s.nozzleTemp, s.nozzleTarget, 300.0f,
                  dispSettings.nozzle.arc, nozzleLabel(s), nullptr, forceRedraw,
                  &dispSettings.nozzle, smoothNozzleTemp, true);

    drawTempGauge(tft, gaugeRight, gaugeY, gR,
                  s.bedTemp, s.bedTarget, 120.0f,
                  dispSettings.bed.arc, "Bed", nullptr, forceRedraw,
                  &dispSettings.bed, smoothBedTemp, true);
  }

  // === "Print Complete" status ===
  if (forceRedraw) {
    tft.setTextDatum(MC_DATUM);
    tft.setTextColor(CLR_GREEN, CLR_BG);
    tft.setTextFont(3);
    tft.drawString("Print Complete", cx, LY_FIN_TEXT_Y);
  }

  // === File name ===
  if (forceRedraw) {
    tft.setTextDatum(MC_DATUM);
    tft.setTextFont(2);
    tft.setTextColor(CLR_TEXT_DIM, CLR_BG);
    if (s.subtaskName[0] != '\0') {
      char truncName[26];
      strncpy(truncName, s.subtaskName, 25);
      truncName[25] = '\0';
      tft.drawString(truncName, cx, LY_FIN_FILE_Y);
    }
  }

  // === kWh used during print (between filename and bottom bar) ===
  bool tasmotaActiveHere = tasmotaIsActiveForSlot(rotState.displayIndex);
  float finishKwh = tasmotaActiveHere ? tasmotaGetPrintKwhUsed() : -1.0f;
  bool kwhChanged = (tasmotaActiveHere && tasmotaKwhChanged()) ||
                    (tasmotaActiveHere != prevFinTasmotaOnline) ||
                    (finishKwh != prevFinKwh);
  if (forceRedraw || kwhChanged) {
    int16_t kwhY = (LY_FIN_FILE_Y + eff_finBotY) / 2;
    tft.fillRect(0, kwhY - 9, scrW, 18, CLR_BG);
    if (tasmotaActiveHere && finishKwh >= 0.0f) {
      drawIcon16(tft, cx - 32, kwhY - 8, icon_lightning, CLR_YELLOW);
      char kwhBuf[16];
      snprintf(kwhBuf, sizeof(kwhBuf), "%.3f kWh", finishKwh);
      tft.setTextDatum(ML_DATUM);
      tft.setTextFont(2);
      tft.setTextColor(CLR_TEXT_DIM, CLR_BG);
      tft.drawString(kwhBuf, cx - 14, kwhY);
    }
  }
  prevFinKwh = finishKwh;

  // === Bottom status bar ===
  bool waitingForDoor = dpSettings.doorAckEnabled && s.doorSensorPresent && !s.doorAcknowledged;
  float finCurWatts = tasmotaGetWatts();
  bool finBottomChanged = forceRedraw ||
                          (waitingForDoor != prevWaitingForDoor) ||
                          (s.doorSensorPresent && s.doorOpen != prevState.doorOpen) ||
                          (tasmotaActiveHere != prevFinTasmotaOnline) ||
                          (finCurWatts != prevFinWatts);
  if (finBottomChanged) {
    prevWaitingForDoor = waitingForDoor;
    tft.fillRect(0, eff_finBotY, scrW, eff_finBotH, CLR_BG);
    tft.setTextFont(1);
    if (waitingForDoor) {
      tft.setTextDatum(MC_DATUM);
      tft.setTextColor(CLR_ORANGE, CLR_BG);
      tft.drawString("Open door to dismiss", cx, eff_finWifiY);
    } else {
      drawIcon16(tft, 4, eff_finWifiY - 8, icon_wifi, CLR_TEXT_DIM);
      tft.setTextDatum(ML_DATUM);
      tft.setTextColor(CLR_TEXT_DIM, CLR_BG);
      char wifiBuf[12];
      snprintf(wifiBuf, sizeof(wifiBuf), "%ddBm", s.wifiSignal);
      tft.drawString(wifiBuf, 22, eff_finWifiY);

      if (tasmotaActiveHere) {
        drawIcon16(tft, cx - 20, eff_finWifiY - 8, icon_lightning, CLR_YELLOW);
        char wBuf[8];
        snprintf(wBuf, sizeof(wBuf), "%.0fW", finCurWatts);
        tft.setTextDatum(ML_DATUM);
        tft.setTextColor(CLR_TEXT_DIM, CLR_BG);
        tft.drawString(wBuf, cx - 2, eff_finWifiY);
      }
    }
    // Door status (right) — always show when sensor present
    if (s.doorSensorPresent) {
      uint16_t clr = s.doorOpen ? CLR_ORANGE : CLR_GREEN;
      tft.setTextDatum(MR_DATUM);
      tft.setTextFont(1);
      tft.setTextColor(clr, CLR_BG);
      tft.drawString("Door", scrW - 20, eff_finWifiY);
      drawIcon16(tft, scrW - 18, eff_finWifiY - 8,
                 s.doorOpen ? icon_unlock : icon_lock, clr);
    }
  }
  prevFinTasmotaOnline = tasmotaActiveHere;
  prevFinWatts = finCurWatts;
}

// ---------------------------------------------------------------------------
//  Night mode — scheduled brightness dimming
// ---------------------------------------------------------------------------
static unsigned long lastNightCheck = 0;
// lastAppliedBrightness declared near setBacklight() above

static bool isNightHour() {
  struct tm now;
  time_t t = time(nullptr);
  localtime_r(&t, &now);
  if (now.tm_year < (2020 - 1900)) return false;  // NTP not synced yet

  uint8_t h = now.tm_hour;
  uint8_t s = dpSettings.nightStartHour;
  uint8_t e = dpSettings.nightEndHour;

  if (s == e) return false;  // same hour = disabled
  if (s < e) return (h >= s && h < e);     // e.g. 01:00-07:00
  return (h >= s || h < e);                // e.g. 22:00-07:00 (wraps midnight)
}

uint8_t getEffectiveBrightness() {
  if (currentScreen == SCREEN_CLOCK) {
    // During night hours, use the dimmer of the two
    if (dpSettings.nightModeEnabled && isNightHour()) {
      return min(dpSettings.screensaverBrightness, dpSettings.nightBrightness);
    }
    return dpSettings.screensaverBrightness;
  }
  if (dpSettings.nightModeEnabled && isNightHour()) {
    return dpSettings.nightBrightness;
  }
  return brightness;
}

void checkNightMode() {
  // Check once per minute
  unsigned long now = millis();
  if (now - lastNightCheck < 60000) return;
  lastNightCheck = now;

  // Don't interfere with screen off
  if (currentScreen == SCREEN_OFF) return;

  uint8_t target = getEffectiveBrightness();
  if (target != lastAppliedBrightness) {
    setBacklight(target);
    lastAppliedBrightness = target;
  }
}

// ---------------------------------------------------------------------------
//  Main update (called from loop)
// ---------------------------------------------------------------------------
void updateDisplay() {
  // Shimmer runs at its own cadence (~40fps), independent of display refresh
  if (currentScreen == SCREEN_PRINTING) {
    BambuState& sh = displayedPrinter().state;
    tickProgressShimmer(tft, 0, sh.progress, sh.printing);
  }
  // Pong clock runs at ~50fps, independent of display refresh
  if (currentScreen == SCREEN_CLOCK && dispSettings.pongClock) {
    tickPongClock();
  }

  unsigned long now = millis();
  unsigned long interval = gaugesAnimating ? GAUGE_ANIM_MS : DISPLAY_UPDATE_MS;
  if (now - lastDisplayUpdate < interval) return;
  lastDisplayUpdate = now;

  // Detect screen change
  if (currentScreen != prevScreen) {
    // Restore backlight when leaving SCREEN_OFF or SCREEN_CLOCK
    if ((prevScreen == SCREEN_OFF || prevScreen == SCREEN_CLOCK) &&
        currentScreen != SCREEN_OFF && currentScreen != SCREEN_CLOCK) {
      setBacklight(getEffectiveBrightness());
    }
    // Reset text size in case Pong clock left it scaled up
    tft.setTextSize(1);
    tft.fillScreen(currentScreen == SCREEN_OFF ? TFT_BLACK : dispSettings.bgColor);
    forceRedraw = true;
    if (currentScreen == SCREEN_CONNECTING_WIFI || currentScreen == SCREEN_CONNECTING_MQTT) {
      connectScreenStart = millis();
    }
    if (currentScreen == SCREEN_CLOCK) {
      if (dispSettings.pongClock) resetPongClock();
      else resetClock();
      setBacklight(getEffectiveBrightness());  // dim for screensaver
    }
    prevScreen = currentScreen;
  }

  switch (currentScreen) {
    case SCREEN_SPLASH:
      // Splash shown in initDisplay(), auto-advance handled by main.cpp
      break;

    case SCREEN_AP_MODE:
      if (forceRedraw) drawAPMode();
      break;

    case SCREEN_CONNECTING_WIFI:
      drawConnectingWiFi();
      break;

    case SCREEN_WIFI_CONNECTED:
      drawWiFiConnected();
      break;

    case SCREEN_CONNECTING_MQTT:
      drawConnectingMQTT();
      break;

#ifdef ENABLE_OTA_AUTO
    case SCREEN_OTA_UPDATE:
      drawOtaUpdate();
      break;
#endif

    case SCREEN_IDLE:
      drawIdle();
      break;

    case SCREEN_PRINTING:
      drawPrinting();
      break;

    case SCREEN_FINISHED:
      drawFinished();
      break;

    case SCREEN_CLOCK:
      if (!dispSettings.pongClock) drawClock();
      // Pong clock is ticked before the throttle (above)
      break;

    case SCREEN_OFF:
      if (forceRedraw) {
        tft.fillScreen(TFT_BLACK);
        setBacklight(0);
        triggerDisplayTransition();  // clear gauge cache so wake shows fresh data
      }
      break;
  }

  // Save state for next smart-redraw comparison
  memcpy(&prevState, &displayedPrinter().state, sizeof(BambuState));
  forceRedraw = false;
}
